PatternAgents/BridgerSoc/BridgerSoc/eagleUp/eagleUp_BridgerSoc_board_bottom.jpg

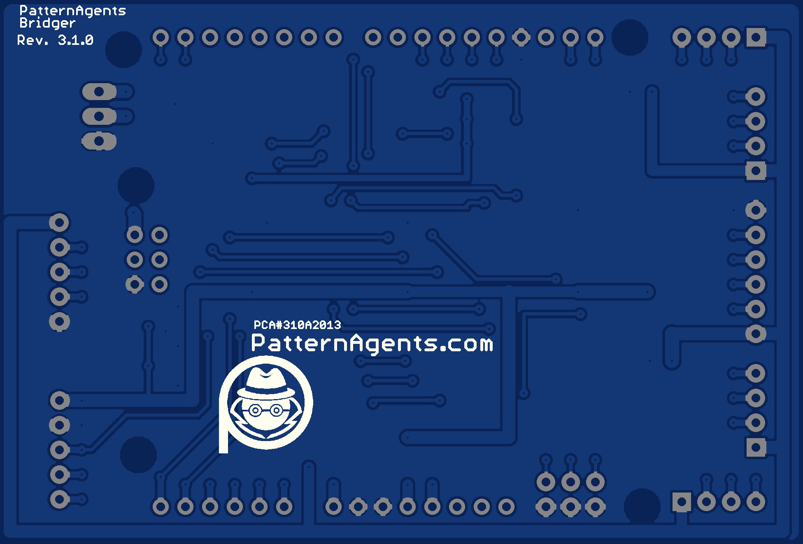
BridgerSoc/eagleUp/eagleUp_BridgerSoc_board_bottom.jpg
