PatternAgents/BridgerSoc/BridgerSoc/eagleUp/eagleUp_BridgerSoc_board_top.jpg

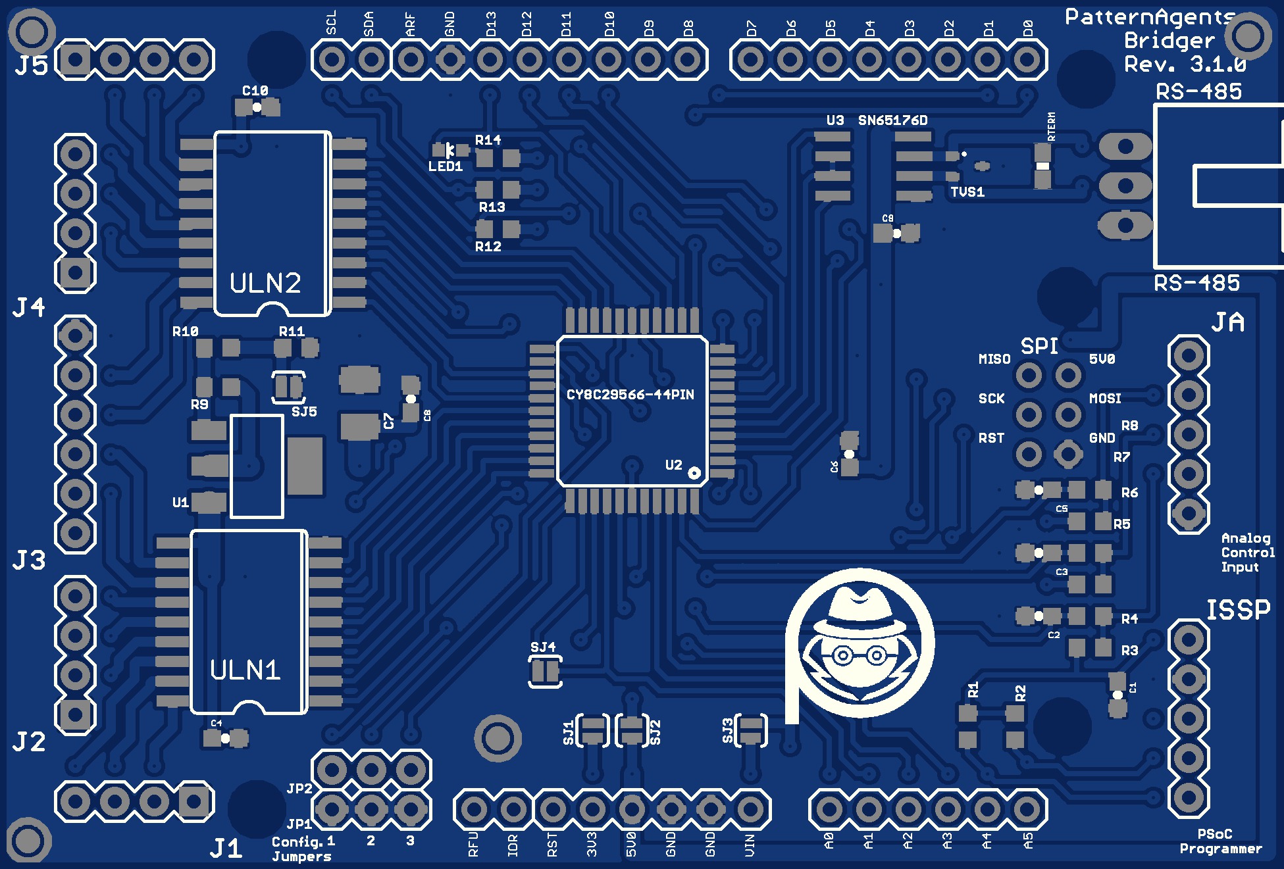
BridgerSoc/eagleUp/eagleUp_BridgerSoc_board_top.jpg
