PatternAgents/BridgerSoc/BridgerSoc/eagleUp/eagleUp_BridgerSoc_bottom.png

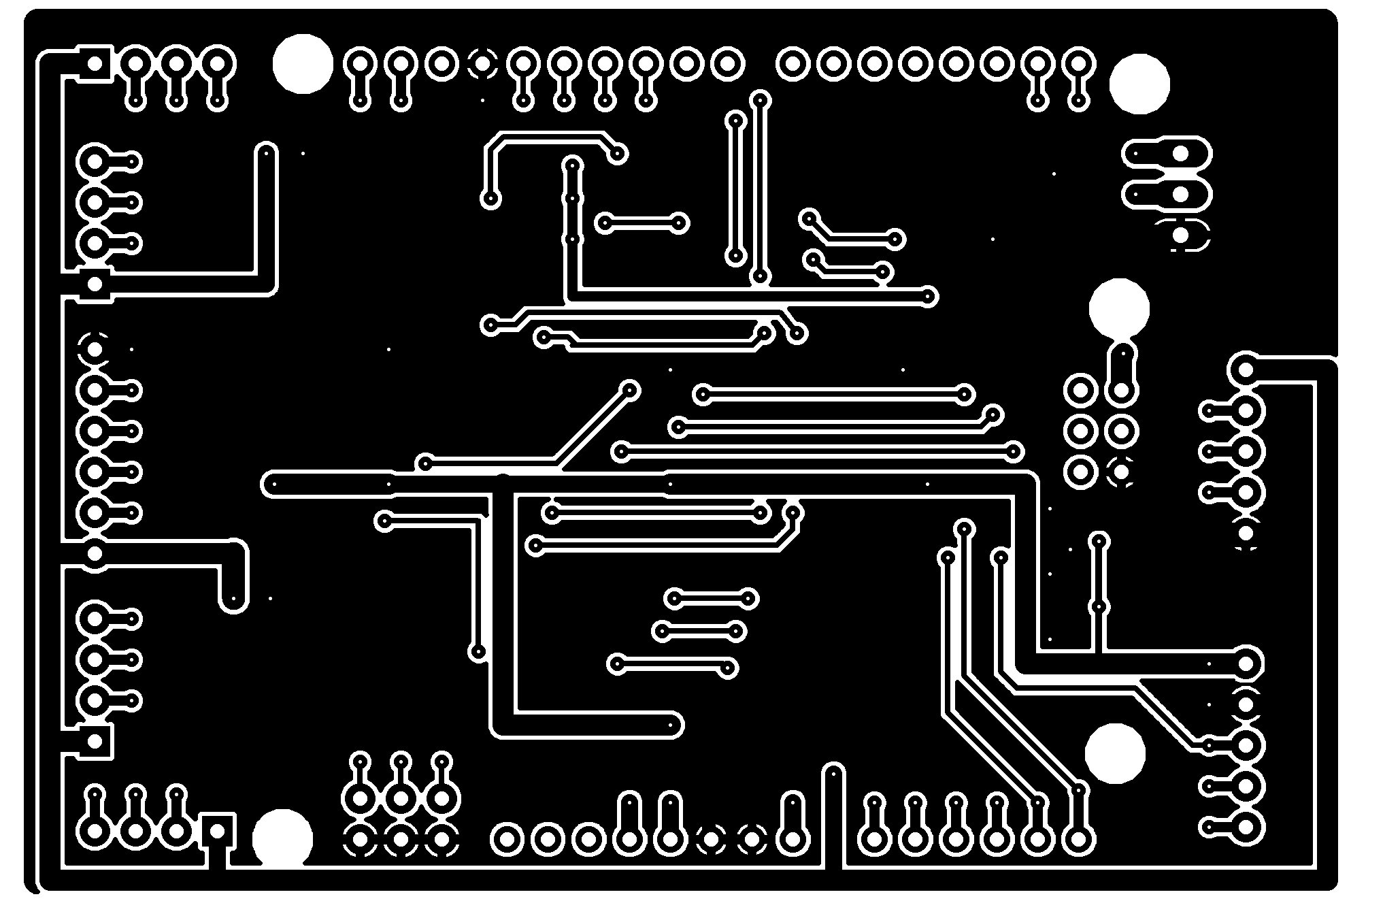
BridgerSoc/eagleUp/eagleUp_BridgerSoc_bottom.png
