PatternAgents/BridgerSoc/BridgerSoc/eagleUp/eagleUp_BridgerSoc_bottom_mask.png

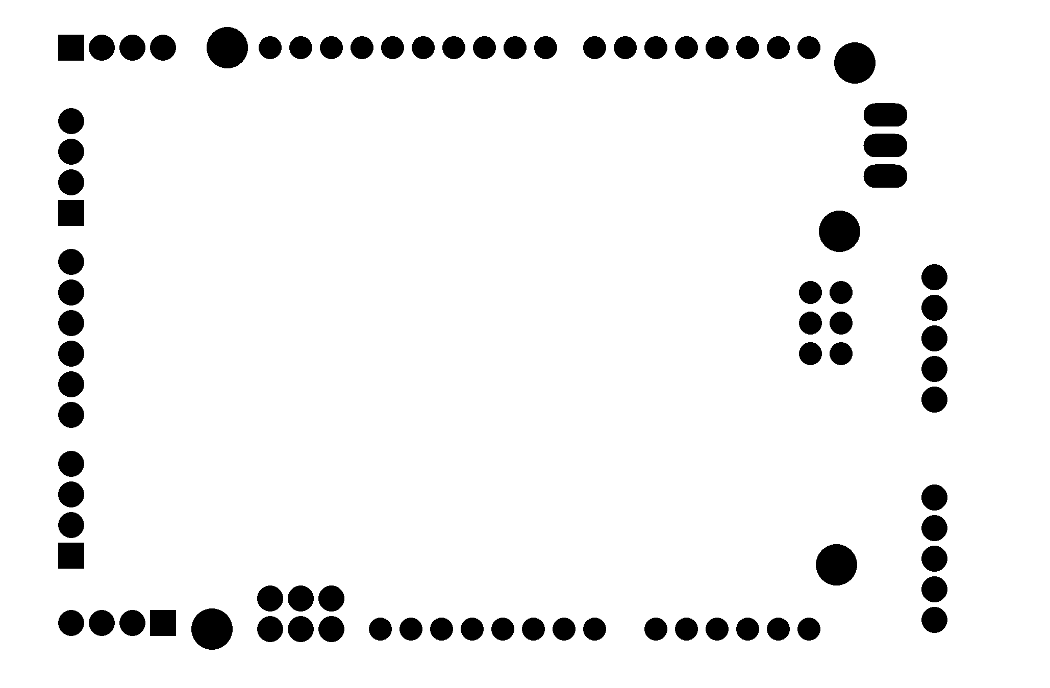
BridgerSoc/eagleUp/eagleUp_BridgerSoc_bottom_mask.png
