PatternAgents/BridgerSoc/BridgerSoc/eagleUp/eagleUp_BridgerSoc_bottom_silk.png

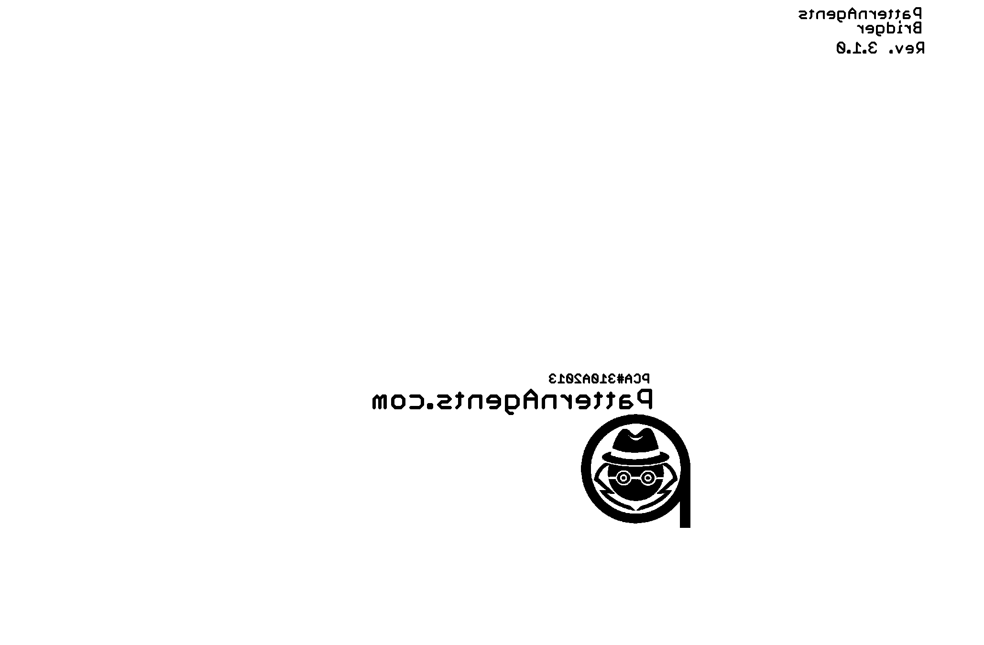
BridgerSoc/eagleUp/eagleUp_BridgerSoc_bottom_silk.png
