PatternAgents/BridgerSoc/BridgerSoc/eagleUp/eagleUp_BridgerSoc_imagesize.png

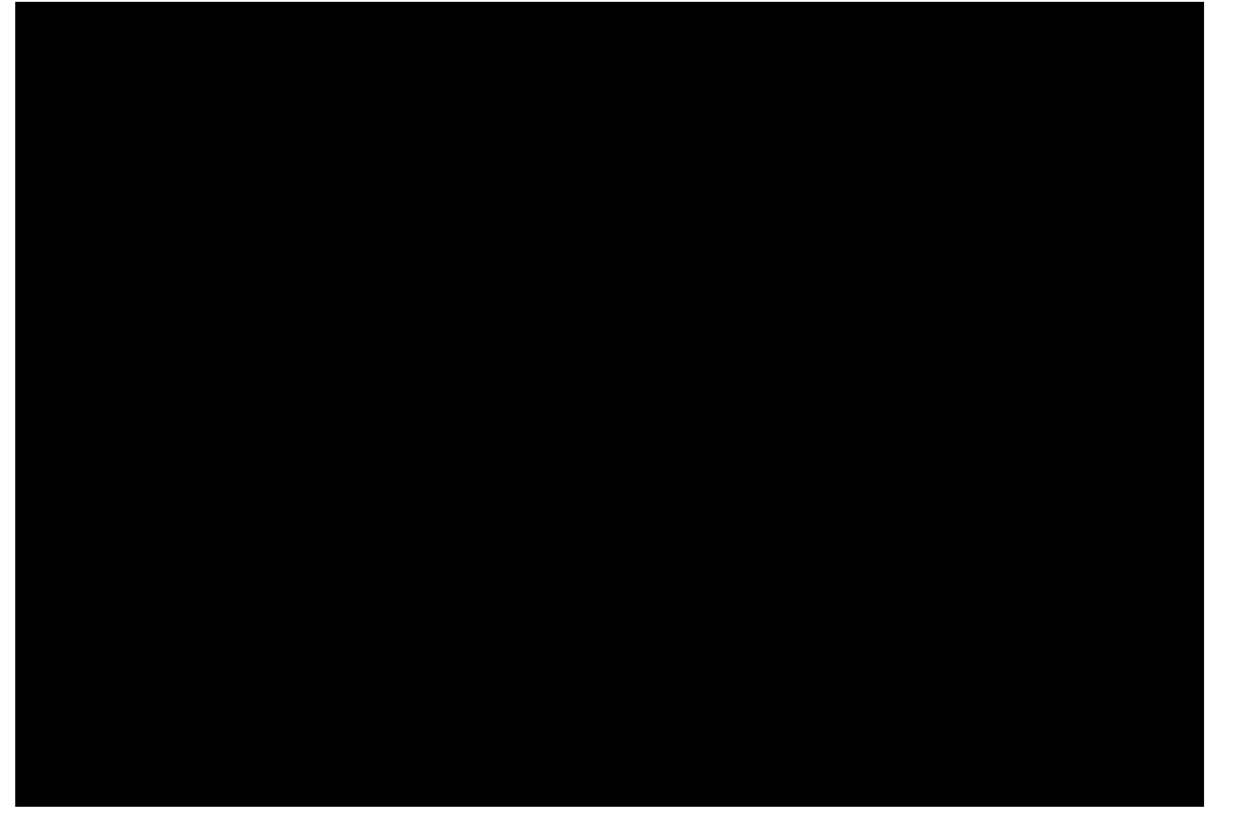
BridgerSoc/eagleUp/eagleUp_BridgerSoc_imagesize.png
