PatternAgents/BridgerSoc/BridgerSoc/eagleUp/eagleUp_BridgerSoc_outline.png

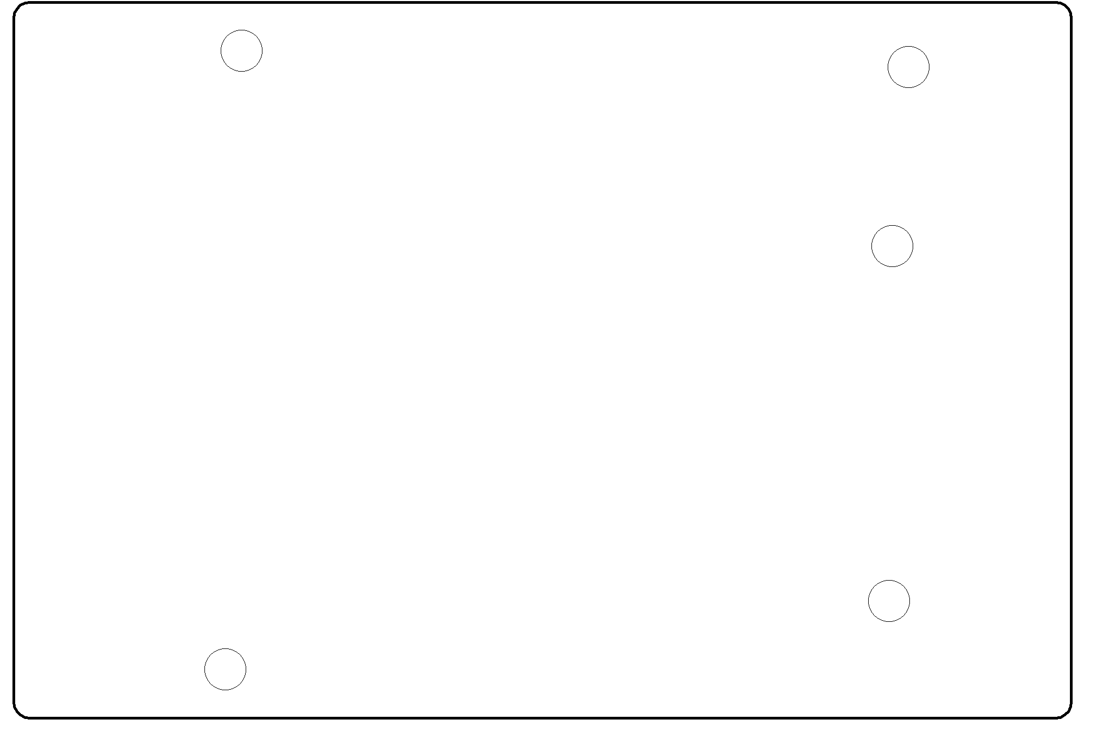
BridgerSoc/eagleUp/eagleUp_BridgerSoc_outline.png
