PatternAgents/BridgerSoc/BridgerSoc/eagleUp/eagleUp_BridgerSoc_top.png

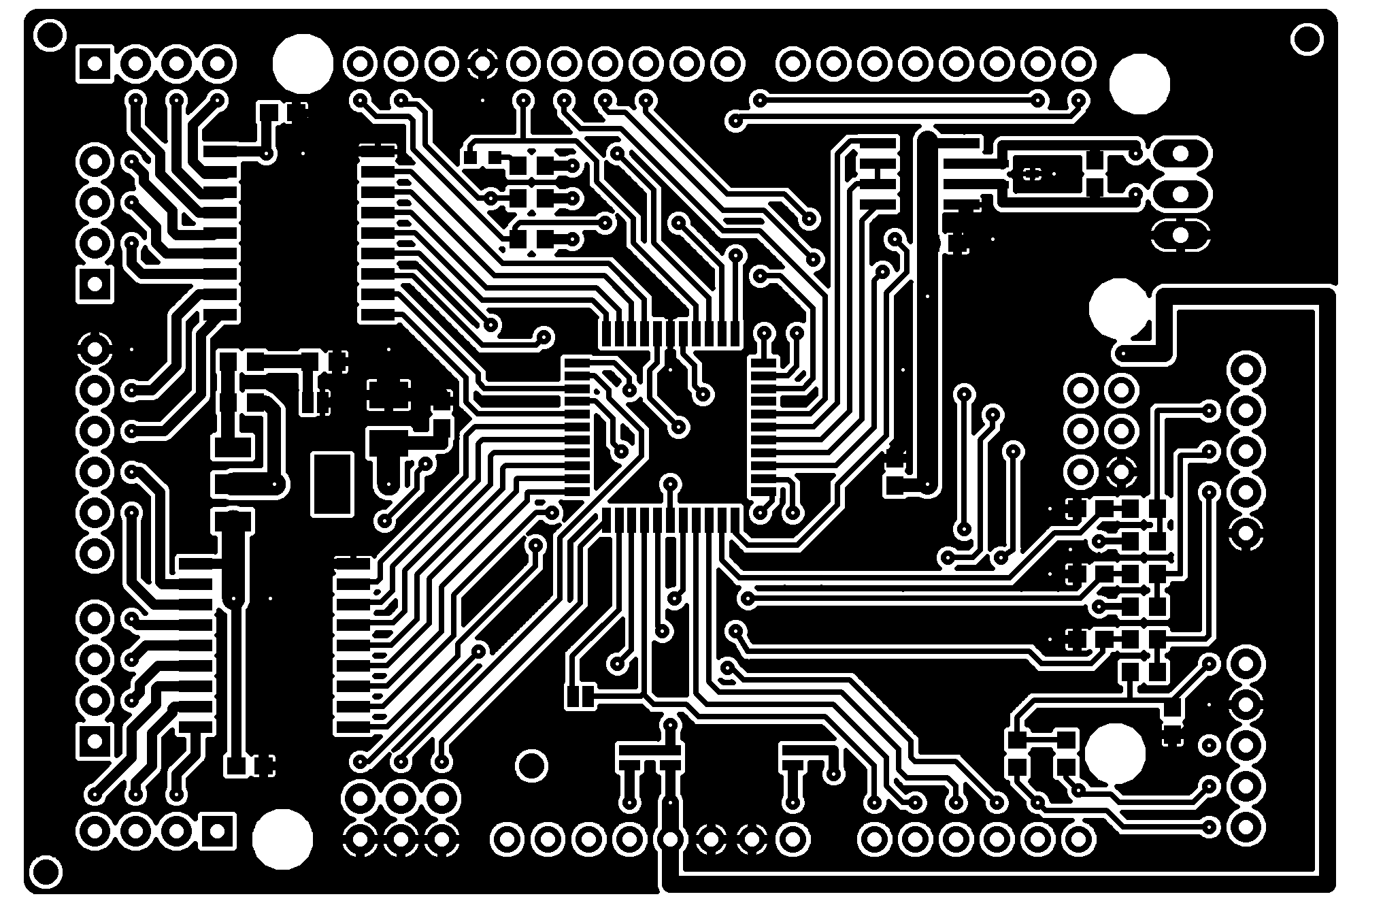
BridgerSoc/eagleUp/eagleUp_BridgerSoc_top.png
