PatternAgents/BridgerSoc/BridgerSoc/eagleUp/eagleUp_BridgerSoc_top_mask.png

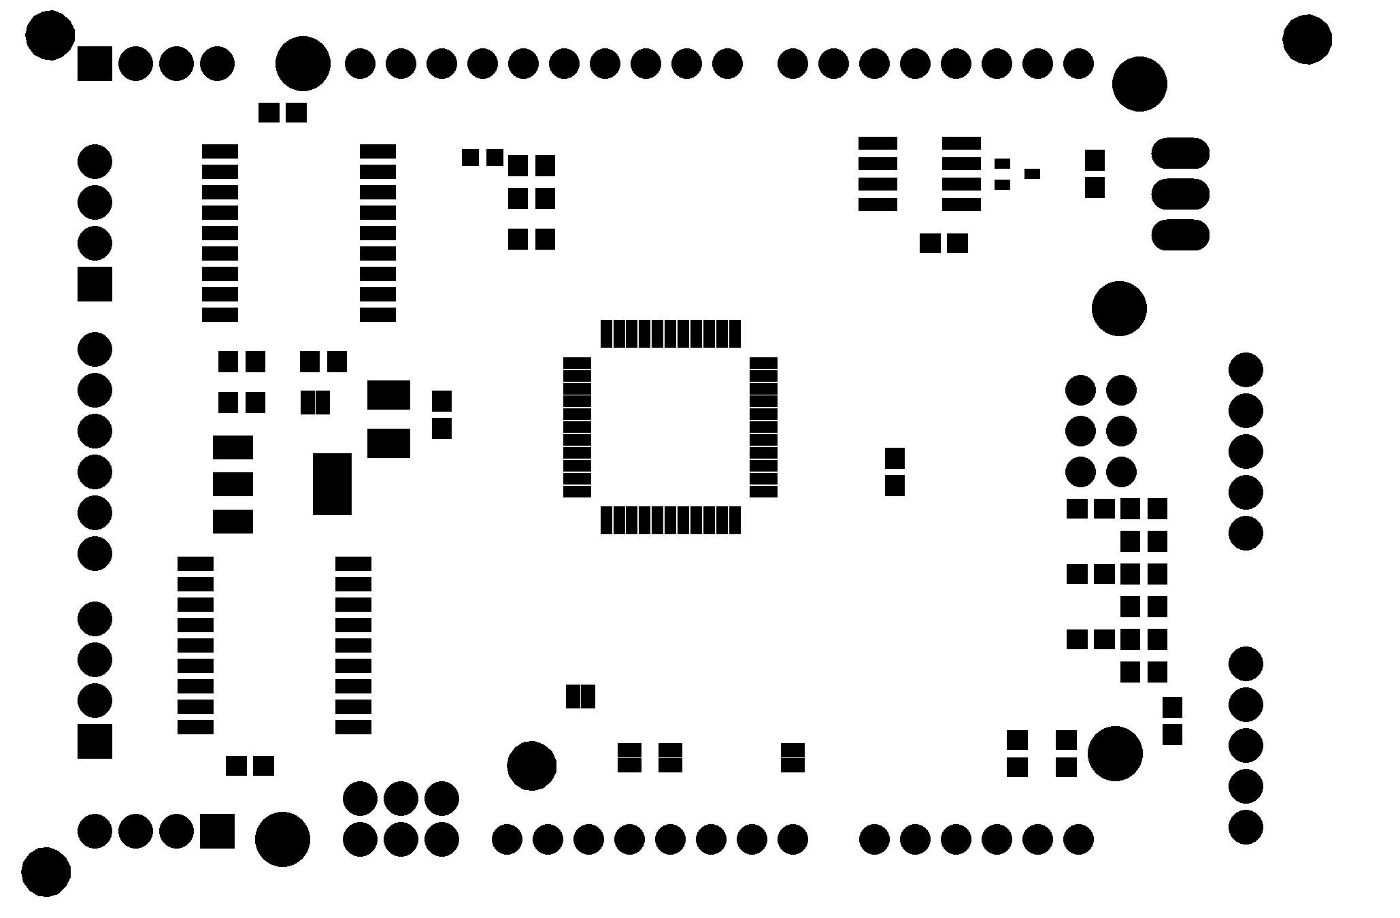
BridgerSoc/eagleUp/eagleUp_BridgerSoc_top_mask.png
