PatternAgents/BridgerSoc/BridgerSoc/eagleUp/eagleUp_BridgerSoc_top_silk.png

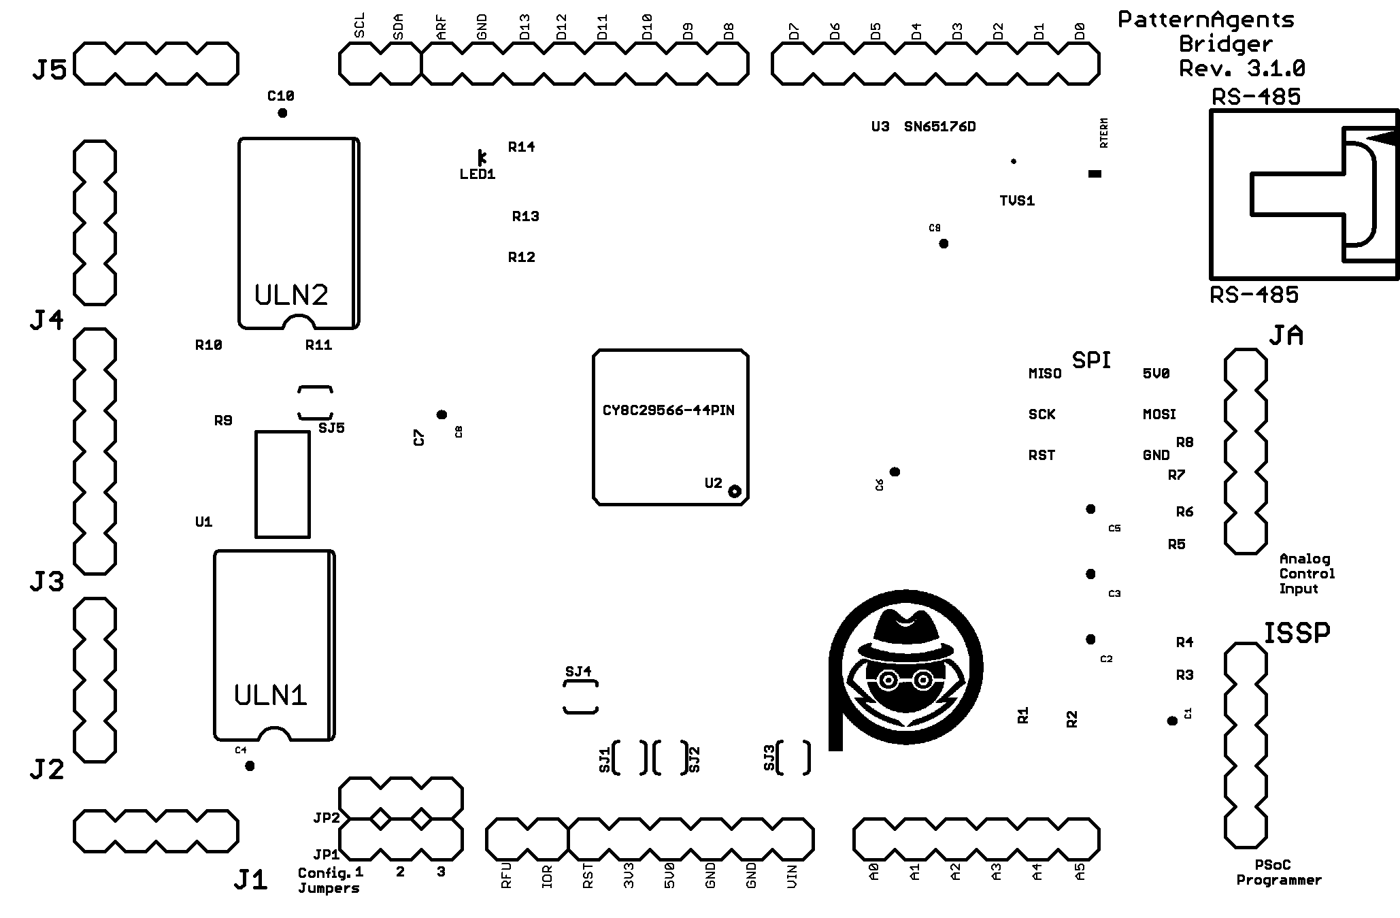
BridgerSoc/eagleUp/eagleUp_BridgerSoc_top_silk.png
