PatternAgents/BridgerSoc/BridgerSoc/images/BridgerSoc_pca.png

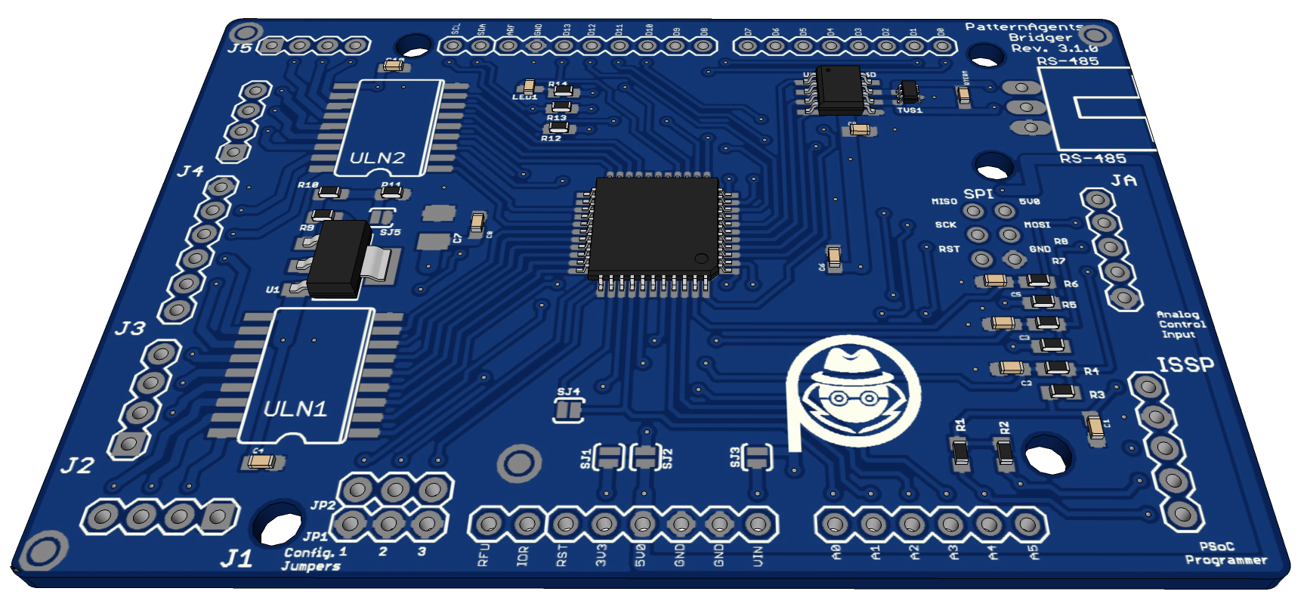
BridgerSoc/images/BridgerSoc_pca.png
